bguan/gugulele/Baritone_Headed_3pc/M4H1R2X2S8T1_FB.scad

include <../G6.scad>;

HIRES = 36; 
DEFRES = 12;
LORES = 4;
SHOW_LOGO = true; 

MODEL = 4;
HEAD_STYLE = 1;
F_GAP = 100;
B_GAP = 100;

USE_SCREWS = true;
SPINE_STYLE = 2;   
SPINE_GAP = 2* NUT_HOLE_GAP;
BRACE_STYLE = 2 ; 
SNDHOLE_STYLE = 8;
TUNER_STYLE = 1;

// string tie style [0-2]
STRTIE_STYLE = 1;

// bigger ratio shorten's the tailend
//FRONT_BACK_RATIO = 2;
//BUTT_CHOP = 20;

// bigger value widen body
//SHOULDER_FLARE = 103;
