bguan/gugulele/Guitar_Decohead_4pc/Guitar_H2R2X1S2T3_FBS.scad

include <../G6.scad>;

// Overriding Default Params
HIRES = 180; 
DEFRES = 60; 
LORES = 20;
SHOW_LOGO = true; 
//SHOW_HEAD = false;
//SHOW_NECK = false;
//SHOW_FRETBD = false;
//SHOW_FRETS = false;
//SHOW_SHOULDER_TOP = false;
//SHOW_SHOULDER_BOTTOM = false;
//SHOW_TOP = false;
//SHOW_BOTTOM = false;
//SHOW_BRIDGE = false;
//SHOW_GUIDE = false;
//SHOW_BRACE = false;
// useful for debugging
//SHOW_PEGS = true;  
//SHOW_STRINGS = true;
//SHOW_SCREWS = true;
//SHOW_SPINE = true;
//SHOW_PICKUP = true;
//SHOW_CUTOUT = true;
//SHOW_CROSS_SECTION = true;

// High level params
TOP_RND_RAD = .5;
BOT_RND_RAD = .5;
HD_RND_RAD = .5;
MODEL = 5;
TUNER_STYLE = 3;
HEAD_STYLE = 2;
SPINE_STYLE = 2;  
SNDHOLE_STYLE = 2; 
BRACE_STYLE = 1;
BRDG_STYLE = 2;
F_GAP = 90;
B_GAP = 90;
S_GAP = 200;
USE_SCREWS = true;
SPINE_GAP = 2*NUT_HOLE_GAP;
FORCE_FRETBD_TANG = true;
FRETBD_LEN = .68*SCALE_LEN;
